manuysys/AGRILION/ModelosPlaquetas_Lanza/Modelo3D_PCB_ArribaLanza/Modelo3D_PCB_ArribaLanza.kicad_sch

## KiCad design ModelosPlaquetas_Lanza/Modelo3D_PCB_ArribaLanza/Modelo3D_PCB_ArribaLanza.kicad_sch (2026-06-07)

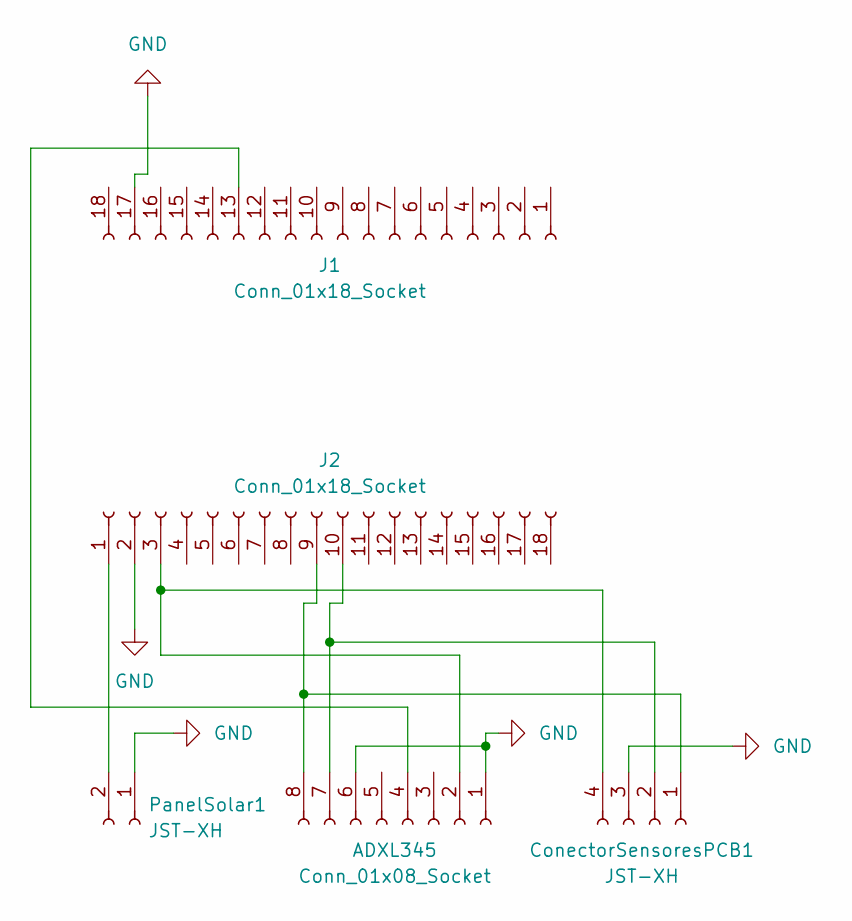
[picture p14: schematic Modelo3D_PCB_ArribaLanza.kicad_sch]

Parts:
ADXL345: Conn_01x08_Socket; PinSocket_1x08_P2.54mm_Vertical
ConectorSensoresPCB1: JST-XH; JST_XH_B4B-XH-A_1x04_P2.50mm_Vertical
J1, J2: Conn_01x18_Socket; PinSocket_1x18_P2.54mm_Vertical
PanelSolar1: JST-XH; JST_XH_B2B-XH-A_1x02_P2.50mm_Vertical

Connections:
GND: ADXL345.1, ADXL345.6, ConectorSensoresPCB1.3, J1.17, J2.2, PanelSolar1.1
unnamed: ADXL345.2, ConectorSensoresPCB1.4, J2.3
unnamed: ADXL345.4, J1.13
unnamed: ADXL345.7, ConectorSensoresPCB1.2, J2.10
unnamed: ADXL345.8, ConectorSensoresPCB1.1, J2.9
unnamed: J2.1, PanelSolar1.2
