manuysys/AGRILION/ModelosPlaquetas_Lanza/Modelo3Ds_PCB1_AbajoLanza/Modelo3Ds_PCBS_AbajoLanza.kicad_sch

## KiCad design ModelosPlaquetas_Lanza/Modelo3Ds_PCB1_AbajoLanza/Modelo3Ds_PCBS_AbajoLanza.kicad_sch (2026-06-07)

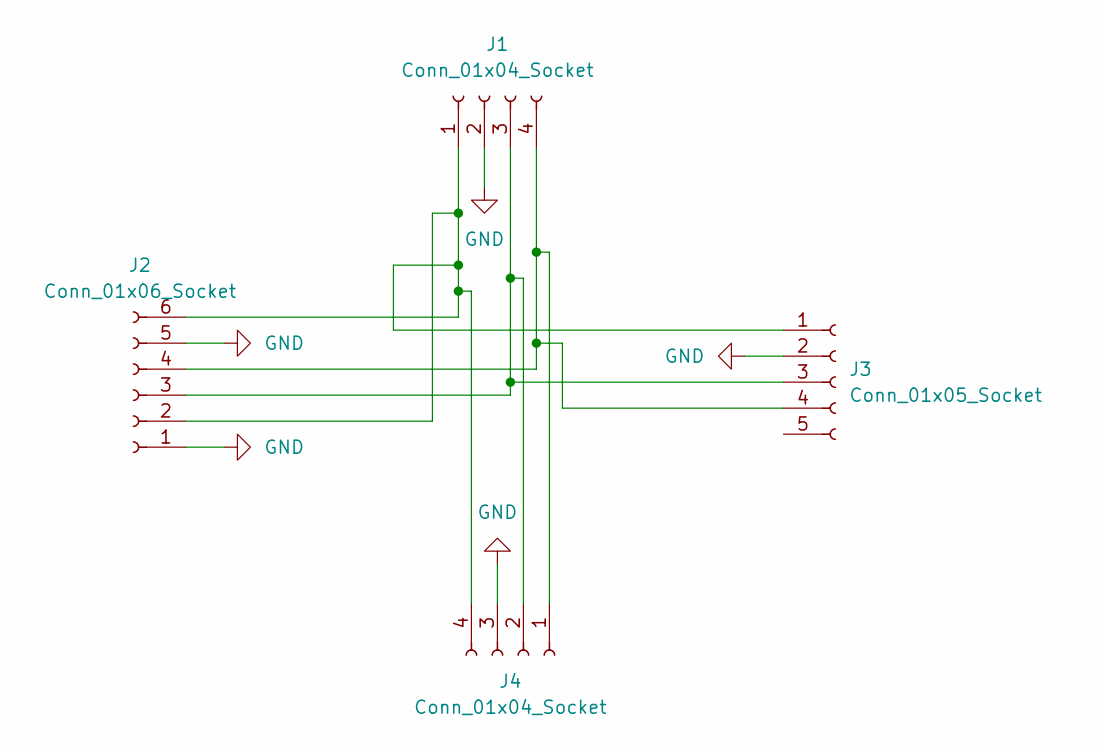
[picture p15: schematic Modelo3Ds_PCBS_AbajoLanza.kicad_sch]

Parts:
J1, J4: Conn_01x04_Socket; JST_XH_B4B-XH-A_1x04_P2.50mm_Vertical
J2: Conn_01x06_Socket; PinSocket_1x06_P2.54mm_Vertical
J3: Conn_01x05_Socket; PinSocket_1x05_P2.54mm_Vertical

Connections:
GND: J1.2, J2.1, J2.5, J3.2, J4.3
unnamed: J1.1, J2.2, J2.6, J3.1, J4.4
unnamed: J1.3, J2.3, J3.3, J4.2
unnamed: J1.4, J2.4, J3.4, J4.1
