manuysys/AGRILION/ModelosPlaquetas_Lanza/Modelo3Ds_PCB2_AbajoLanza/Modelo3Ds_PCB2_AbajoLanza.kicad_sch

## KiCad design ModelosPlaquetas_Lanza/Modelo3Ds_PCB2_AbajoLanza/Modelo3Ds_PCB2_AbajoLanza.kicad_sch (2026-06-07)

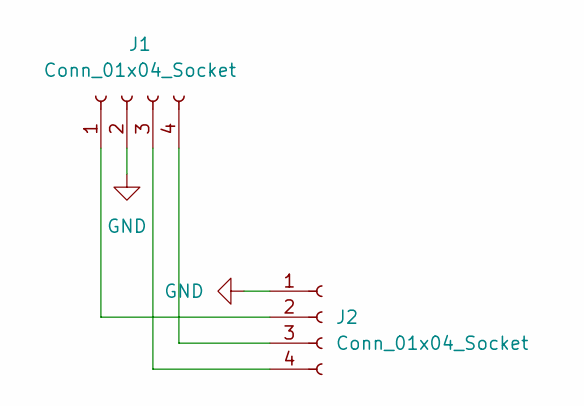
[picture p16: schematic Modelo3Ds_PCB2_AbajoLanza.kicad_sch]

Parts:
J1: Conn_01x04_Socket; JST_XH_B4B-XH-A_1x04_P2.50mm_Vertical
J2: Conn_01x04_Socket; PinSocket_1x04_P2.54mm_Vertical

Connections:
GND: J1.2, J2.1
unnamed: J1.1, J2.2
unnamed: J1.3, J2.4
unnamed: J1.4, J2.3
